Tymut/Moon60/1.0/Ergopad/Main/1/8.jpeg

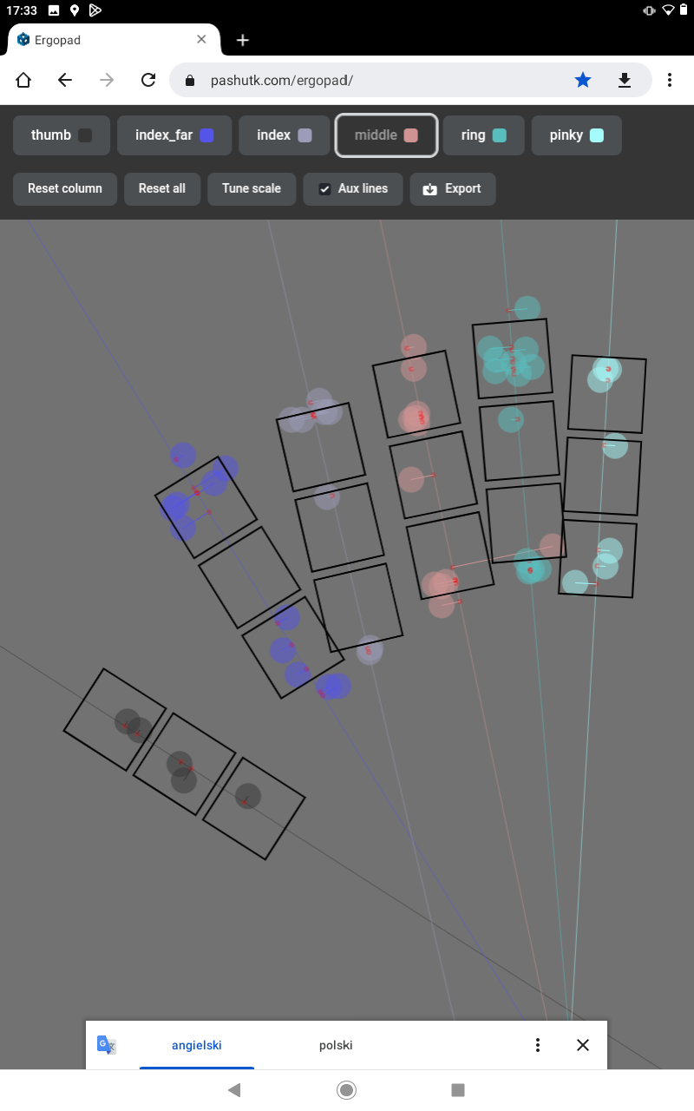
1.0/Ergopad/Main/1/8.jpeg
