Tymut/Moon60/1.0/Ergopad/Main/1/10.jpeg

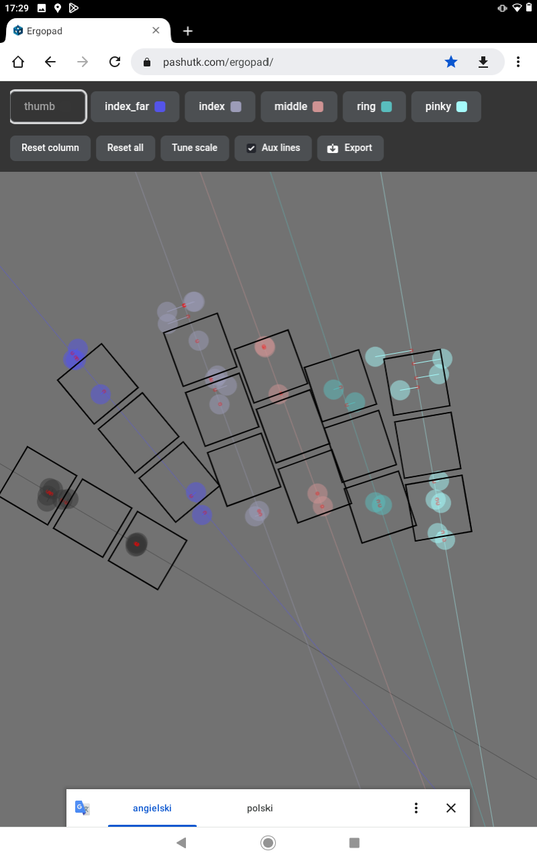
1.0/Ergopad/Main/1/10.jpeg
