Tymut/Moon60/1.0/Ergopad/Main/2/2.jpeg

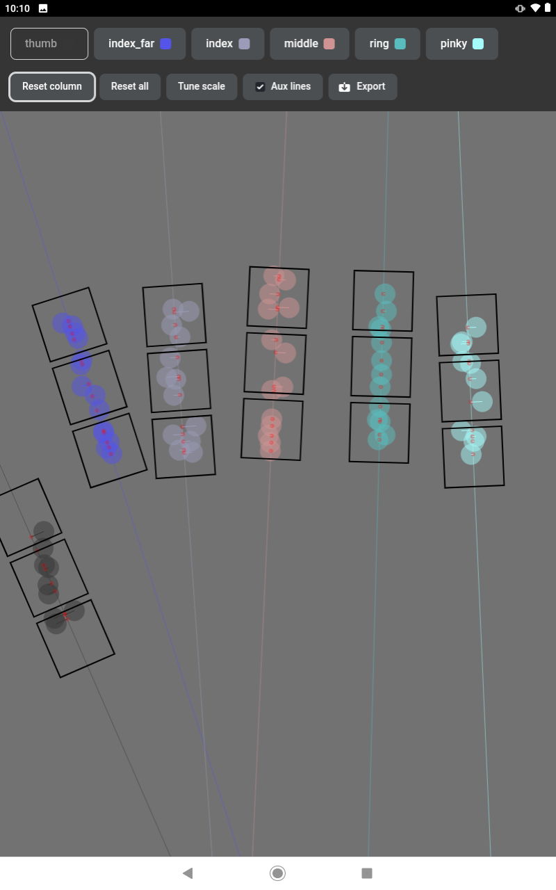
1.0/Ergopad/Main/2/2.jpeg
