Tymut/Moon60/1.0/Ergopad/Main/2/4.jpeg

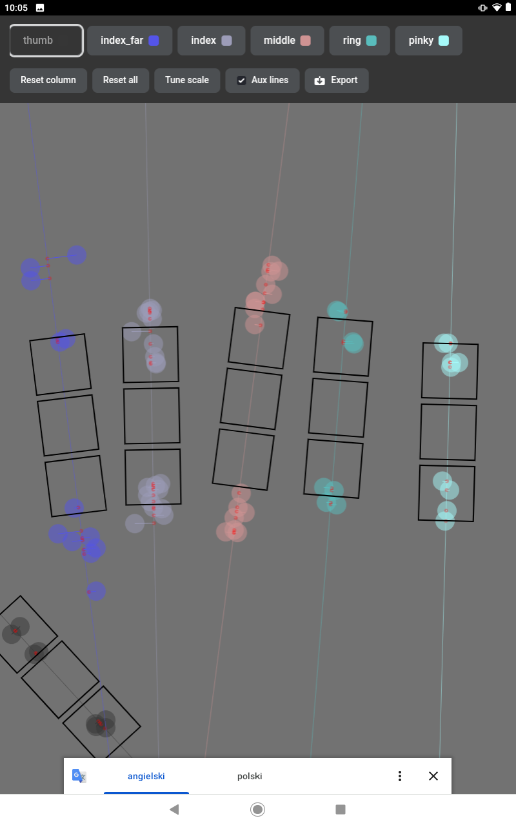
1.0/Ergopad/Main/2/4.jpeg
