Tymut/Moon60/1.0/Ergopad/Main/3/3.jpeg

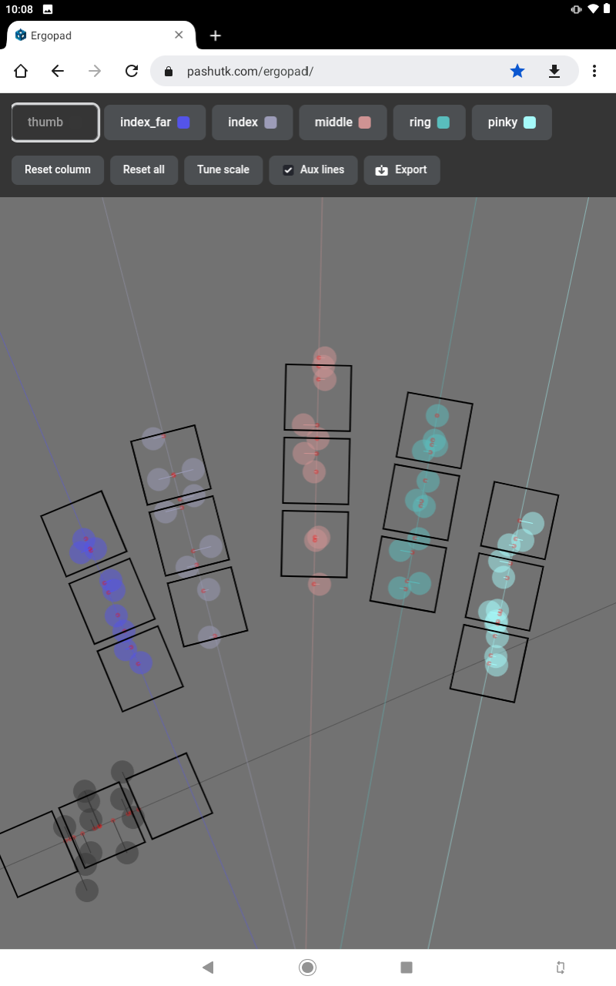
1.0/Ergopad/Main/3/3.jpeg
