Tymut/Moon60/1.0/Ergopad/Main/3/14.jpeg

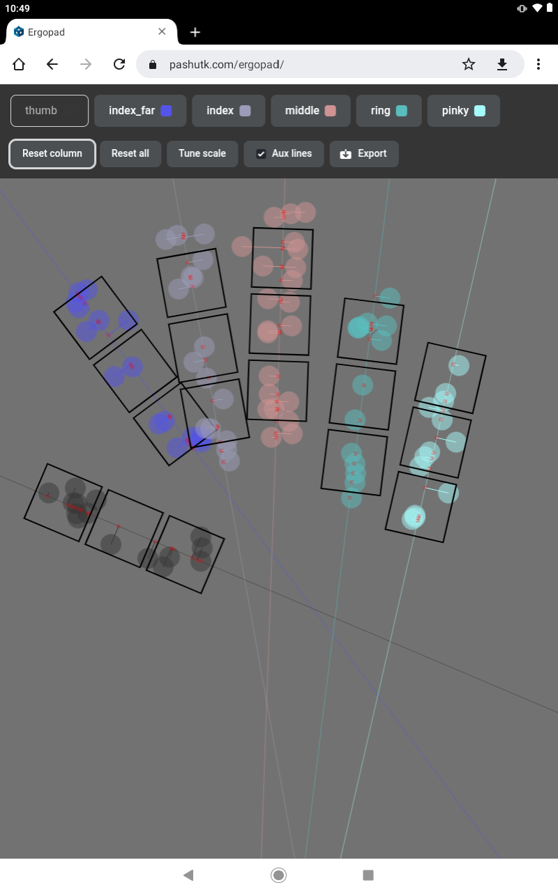
1.0/Ergopad/Main/3/14.jpeg
