Tymut/Moon60/1.0/Ergopad/Main/3/15.jpeg

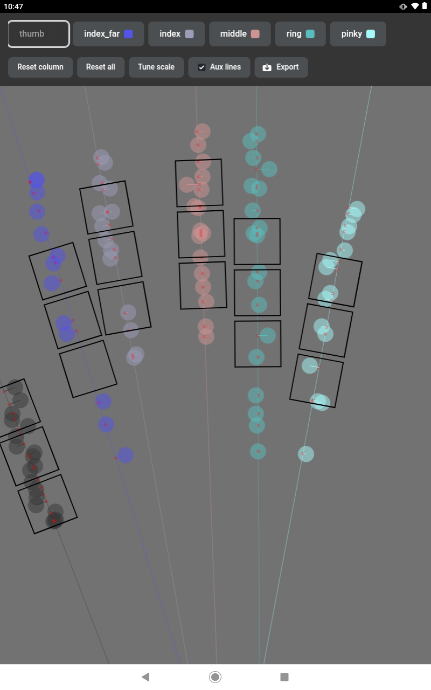
1.0/Ergopad/Main/3/15.jpeg
