Tymut/Moon60/1.0/Ergopad/Main/4/6.jpeg

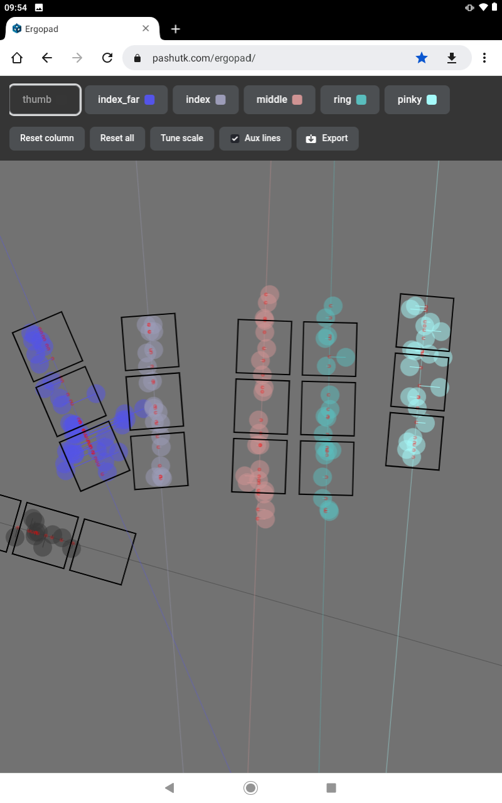
1.0/Ergopad/Main/4/6.jpeg
