Tymut/Moon60/1.0/Ergopad/Main/4/7.jpeg

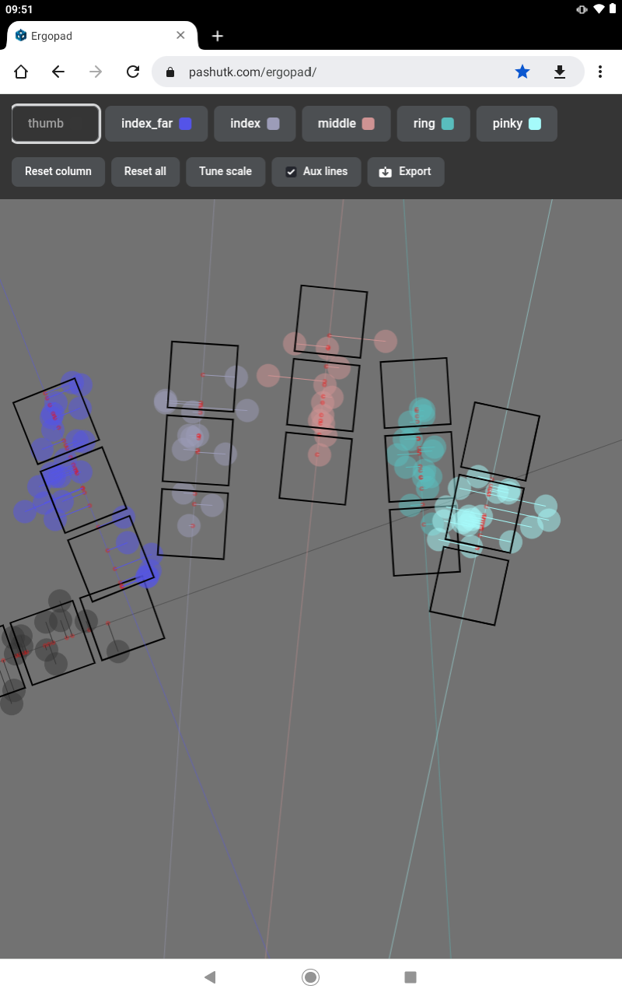
1.0/Ergopad/Main/4/7.jpeg
