Tymut/Moon60/1.0/Ergopad/Main/4/9.jpeg

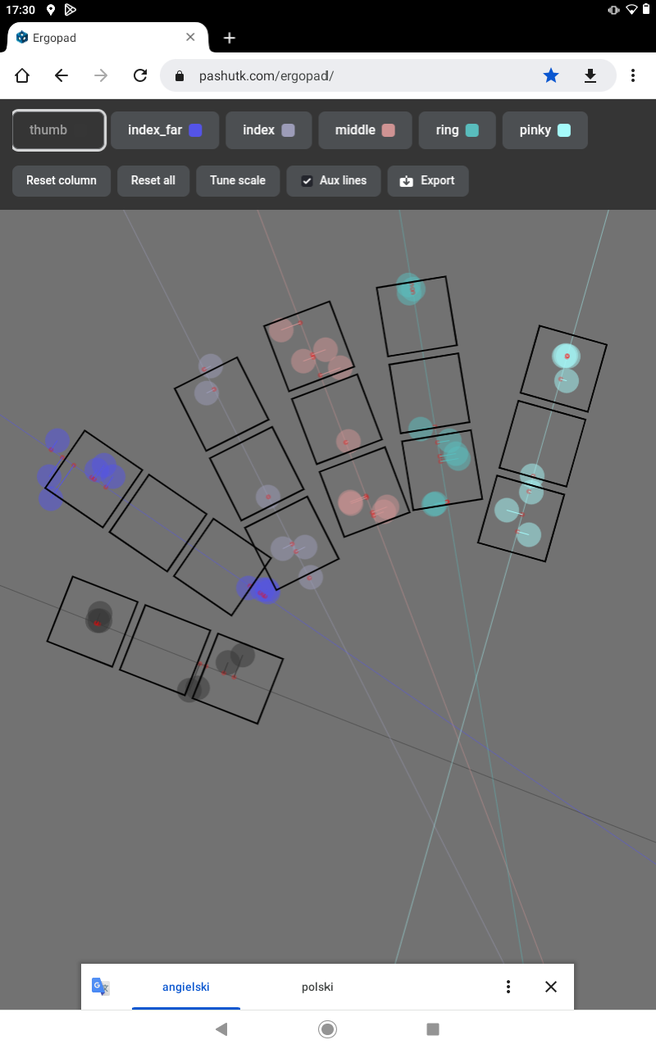
1.0/Ergopad/Main/4/9.jpeg
