Tymut/Moon60/1.0/Ergopad/Main/4/12.jpeg

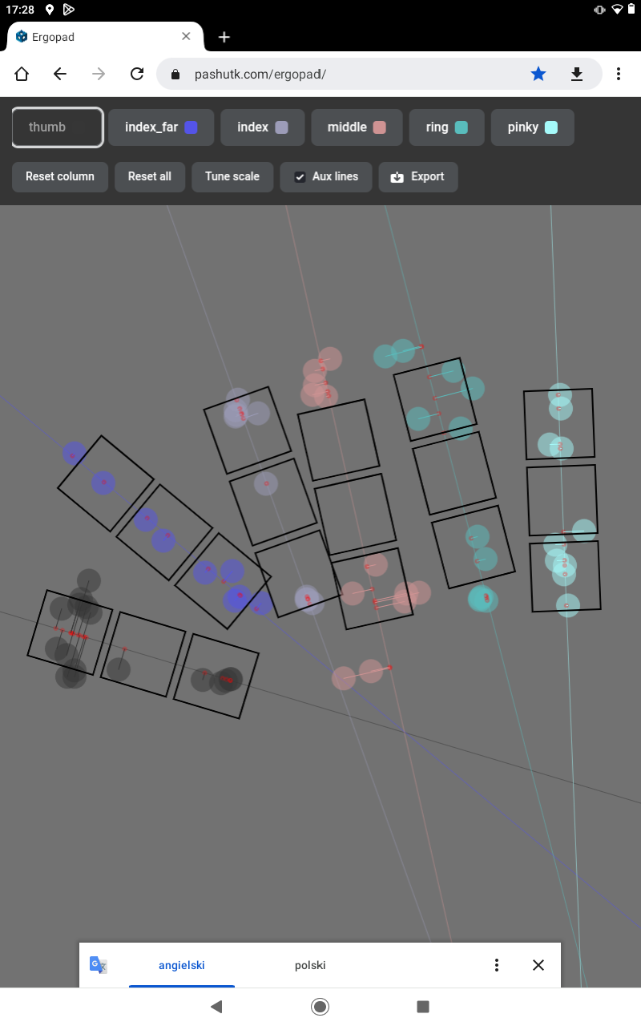
1.0/Ergopad/Main/4/12.jpeg
