Tymut/Moon60/1.0/Ergopad/Main/1/Result/result1.png

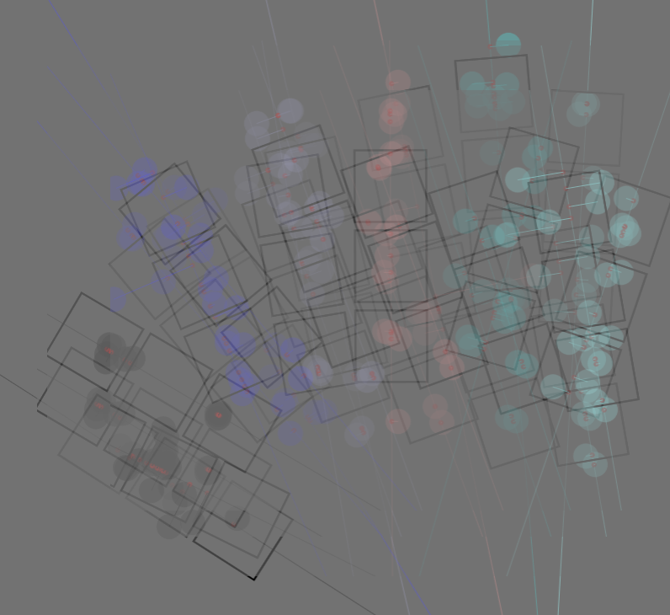
1.0/Ergopad/Main/1/Result/result1.png
