Tymut/Moon60/1.0/Ergopad/Main/2/Result/result2.png

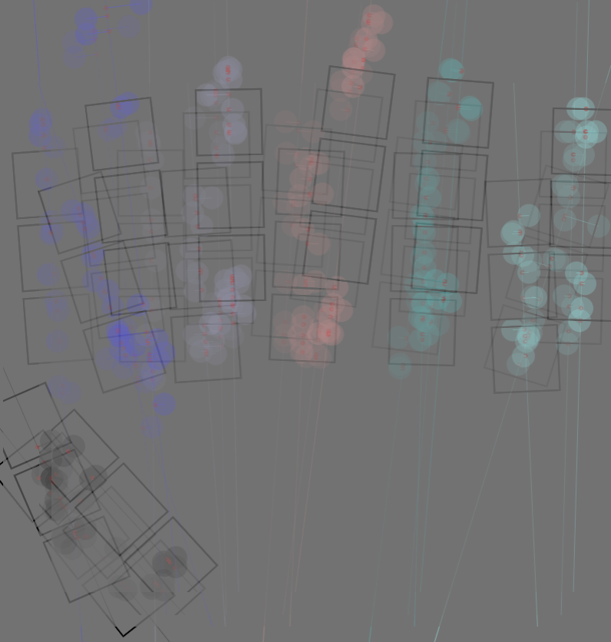
1.0/Ergopad/Main/2/Result/result2.png
