Tymut/Moon60/1.0/Ergopad/Main/3/Result/result3.png

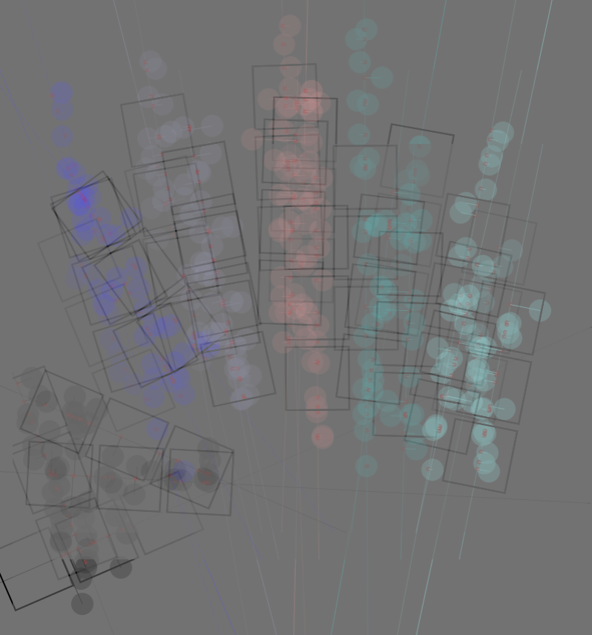
1.0/Ergopad/Main/3/Result/result3.png
