Tymut/Moon60/1.0/Ergopad/Main/4/Result/result4.png

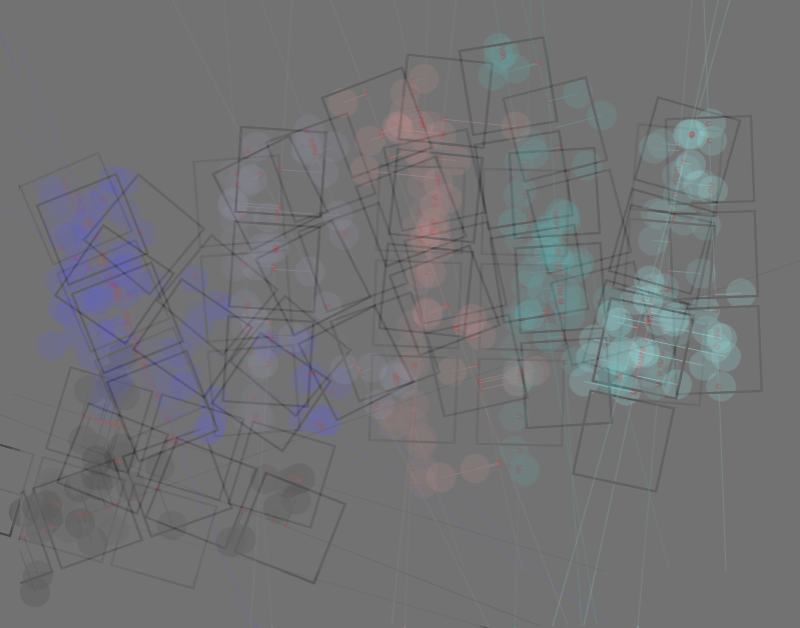
1.0/Ergopad/Main/4/Result/result4.png
