Tymut/Moon60/1.0/Ergopad/Mirror/1/Result/result1_mirror.png

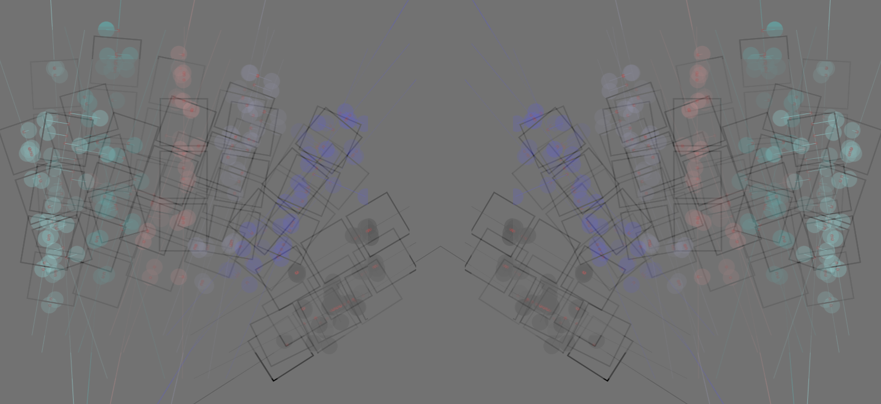
1.0/Ergopad/Mirror/1/Result/result1_mirror.png
