Tymut/Moon60/1.0/Ergopad/Mirror/2/Result/result2_mirror.png

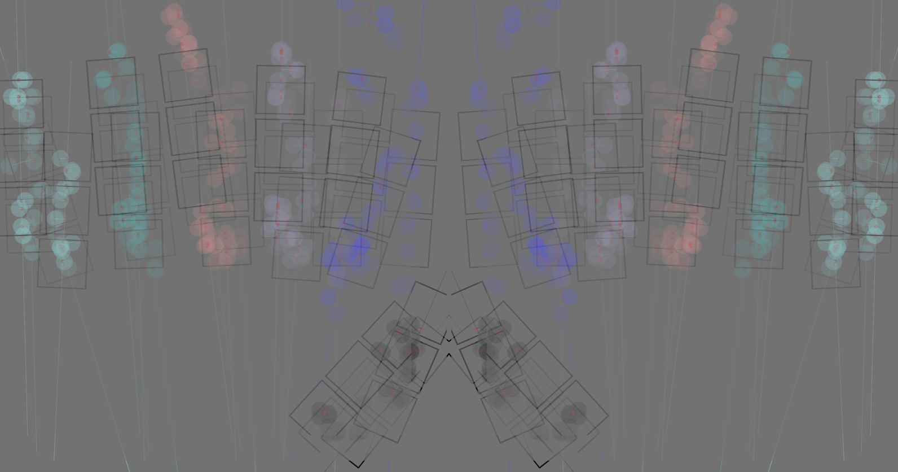
1.0/Ergopad/Mirror/2/Result/result2_mirror.png
