Tymut/Moon60/1.0/Ergopad/Mirror/3/Result/result3_mirror.png

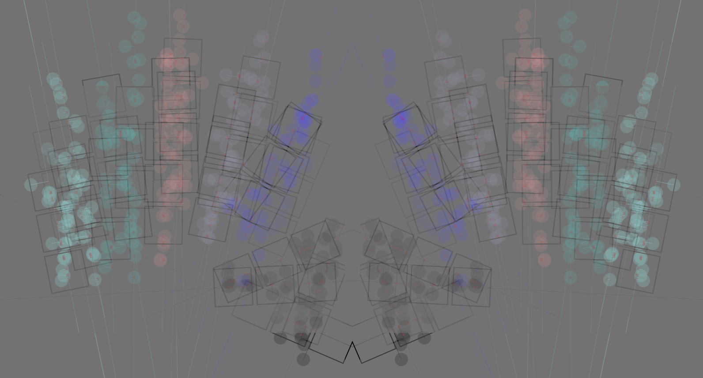
1.0/Ergopad/Mirror/3/Result/result3_mirror.png
