Tymut/Moon60/1.0/Ergopad/Mirror/4/Result/result4_mirror.png

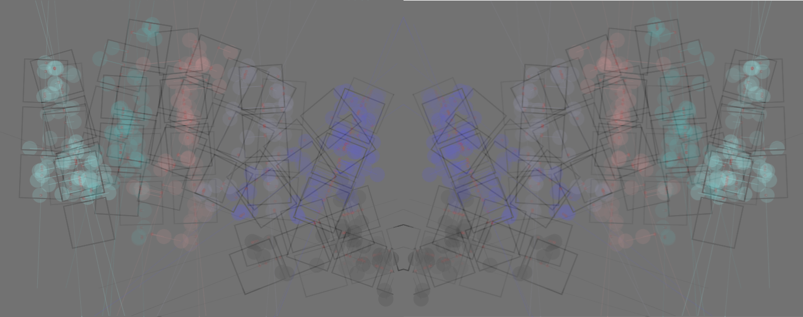
1.0/Ergopad/Mirror/4/Result/result4_mirror.png
